Karmaleon0/Solar_nRF/HW/SIMS/astableMultivibrator.asc

C1: cap; 10n
C2: cap; 10n
C3: cap; 1µ
C4: cap; 1µ
C5: cap; 1µ
C6: cap; 1µ
C10: cap; 1n
D1: diode; 1N5817
D2: diode; 1N5817
D3: diode; 1N5817
D4: diode; 1N5817
D5: diode; 1N5817
Q1: npn; BC847C
Q2: npn; BC847C
Q3: npn; BC847C
R1: res; 120k
R2: res; 120k
R3: res; 1k
R4: res; 1k
R5: res; 120k
R6: res; 1Meg
R7: res; 470k
V1: voltage; 3; Rser=1000
Named nets: 0
.tran 0.2
